Shao-TX/TKUECE-Dessertation/images/limited_switch.jpg

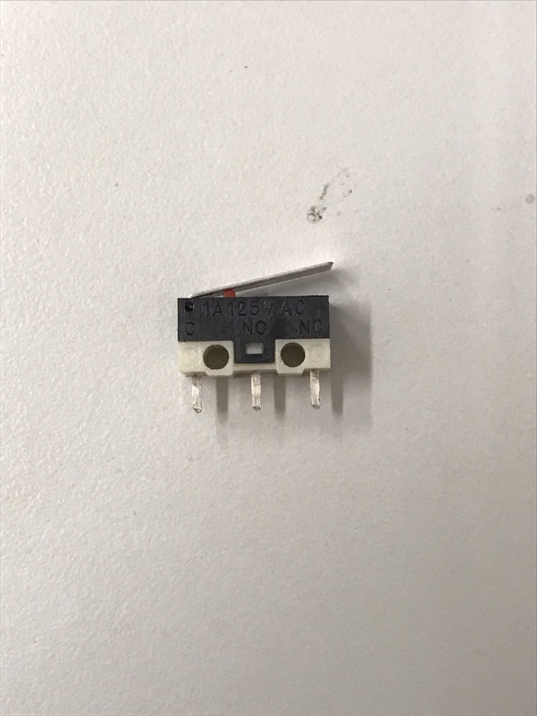
images/limited_switch.jpg
