Shao-TX/TKUECE-Dessertation/images/PCB.jpg

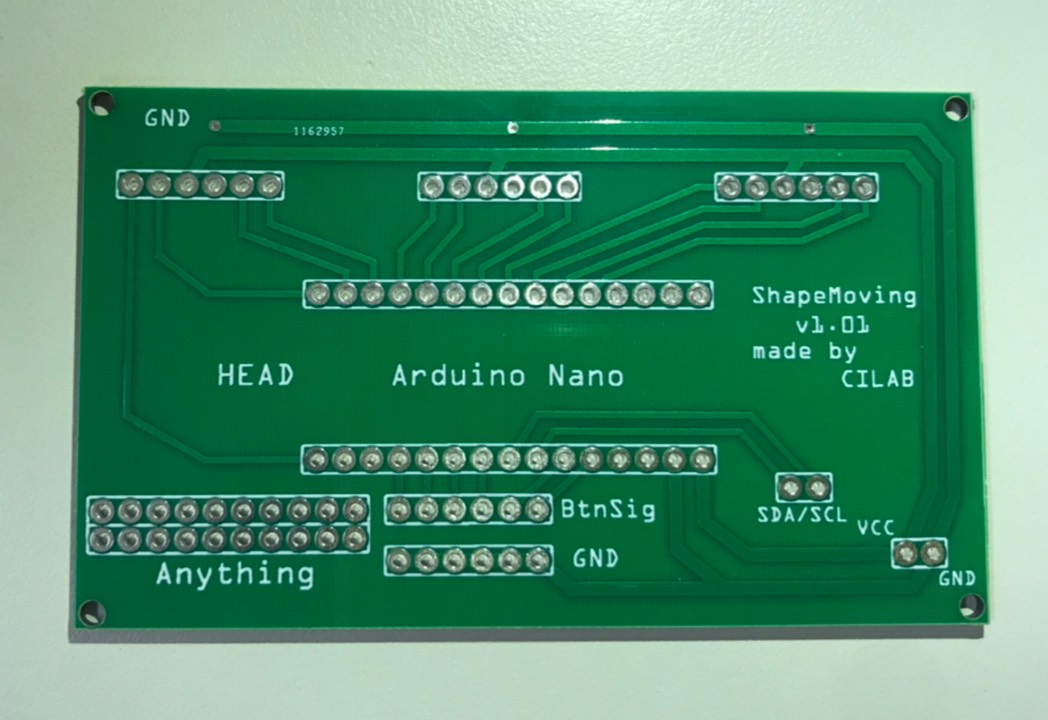
images/PCB.jpg
