Shao-TX/TKUECE-Dessertation/software/Arduino/main_code.ino

#define A1_A 13
#define A1_B 11
#define A2_A 12
#define A2_B 10
#define A3_A 8
#define A3_B 9
#define A4_A 7
#define A4_B 6
#define A5_A 4
#define A5_B 5
#define A6_A 2
#define A6_B 3

void motor_stop();
void motor_action(int key);

void setup() {
  Serial.begin(9600);

  // PIN 設定
  pinMode(A1_A,OUTPUT);
  pinMode(A1_B,OUTPUT);
  pinMode(A2_A,OUTPUT);
  pinMode(A2_B,OUTPUT);
  pinMode(A3_A,OUTPUT);
  pinMode(A3_B,OUTPUT);
  pinMode(A4_A,OUTPUT);
  pinMode(A4_B,OUTPUT);
  pinMode(A5_A,OUTPUT);
  pinMode(A5_B,OUTPUT);
  pinMode(A6_A,OUTPUT);
  pinMode(A6_B,OUTPUT);

  // PIN 初始
  digitalWrite(A1_A,LOW);
  digitalWrite(A1_B,LOW);
  digitalWrite(A2_A,LOW);
  digitalWrite(A2_B,LOW);
  digitalWrite(A3_A,LOW);
  digitalWrite(A3_B,LOW);
  digitalWrite(A4_A,LOW);
  digitalWrite(A4_B,LOW);
  digitalWrite(A5_A,LOW);
  digitalWrite(A5_B,LOW);
  digitalWrite(A6_A,LOW);
  digitalWrite(A6_B,LOW);
}

void loop() {

  motor_stop();
  
  if(Serial.available()){         
    int x = Serial.parseInt();
    if(x == 20){
      motor_action(x);
      }
    motor_forward(x);
    motor_back(x);
    Serial.println(x);
   }
}


void motor_stop(){
  digitalWrite(A1_A,LOW);
  digitalWrite(A1_B,LOW);
  digitalWrite(A2_A,LOW);
  digitalWrite(A2_B,LOW);
  digitalWrite(A3_A,LOW);
  digitalWrite(A3_B,LOW);
  digitalWrite(A4_A,LOW);
  digitalWrite(A4_B,LOW);
  digitalWrite(A5_A,LOW);
  digitalWrite(A5_B,LOW);
  digitalWrite(A6_A,LOW);
  digitalWrite(A6_B,LOW);
}


void motor_forward(int key1){
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
   digitalWrite(A5_B,LOW);
   delay(delay_time);
   analogWrite(A5_A,LOW);
   digitalWrite(A5_B,255);
   delay(delay_time);

   analogWrite(A6_A,255);
   digitalWrite(A6_B,LOW);
   delay(delay_time);
   analogWrite(A6_A,LOW);
   digitalWrite(A6_B,255);
   delay(delay_time);
}
